CapableRobot/SenseTemp/revisions/CREAES/SenseTemp - CREAES.png

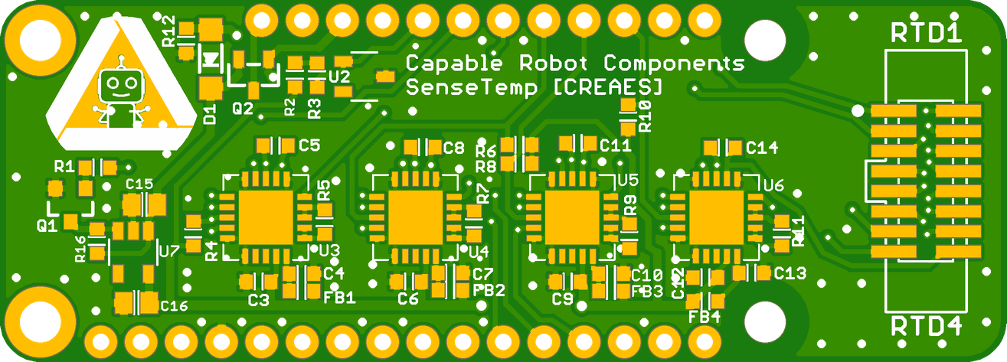
revisions/CREAES/SenseTemp - CREAES.png
